bradsprojects/Digirule2U/Firmware/Source/Digirule2.X/file.c

#include "digirule2.h"

static const uint8 __section( "files" ) files[8][256] =
{
	// Slot 0 "HELLO WORLD"
	{
		0x02, 0x01, 0x05, 0x20, 0x06, 0x09, 0x00, 0x26, 
		0x00, 0xFC, 0x28, 0x02, 0xC0, 0x1E, 0x06, 0x28, 
		0x05, 0x00, 0x00, 0x00, 0x00, 0x00, 0x00, 0x00, 
		0x00, 0x00, 0x00, 0x00, 0x00, 0x00, 0x00, 0x00, 
		0x0D, 0x0A, 0x20, 0x5F, 0x20, 0x20, 0x5F, 0x20, 
		0x20, 0x20, 0x20, 0x20, 0x5F, 0x20, 0x5F, 0x20, 
		0x20, 0x20, 0x20, 0x20, 0x20, 0x5F, 0x5F, 0x20, 
		0x20, 0x20, 0x20, 0x20, 0x20, 0x5F, 0x5F, 0x20, 
		0x20, 0x20, 0x20, 0x20, 0x20, 0x20, 0x5F, 0x20, 
		0x20, 0x20, 0x20, 0x5F, 0x20, 0x20, 0x20, 0x5F, 
		0x20, 0x0D, 0x0A, 0x7C, 0x20, 0x7C, 0x7C, 0x20, 
		0x7C, 0x5F, 0x5F, 0x5F, 0x7C, 0x20, 0x7C, 0x20, 
		0x7C, 0x5F, 0x5F, 0x5F, 0x20, 0x20, 0x5C, 0x20, 
		0x5C, 0x20, 0x20, 0x20, 0x20, 0x2F, 0x20, 0x2F, 
		0x5F, 0x5F, 0x20, 0x5F, 0x20, 0x5F, 0x7C, 0x20, 
		0x7C, 0x5F, 0x5F, 0x7C, 0x20, 0x7C, 0x20, 0x7C, 
		0x20, 0x7C, 0x0D, 0x0A, 0x7C, 0x20, 0x5F, 0x5F, 
		0x20, 0x2F, 0x20, 0x2D, 0x5F, 0x29, 0x20, 0x7C, 
		0x20, 0x2F, 0x20, 0x5F, 0x20, 0x5C, 0x20, 0x20, 
		0x5C, 0x20, 0x5C, 0x2F, 0x5C, 0x2F, 0x20, 0x2F, 
		0x20, 0x5F, 0x20, 0x5C, 0x20, 0x27, 0x5F, 0x7C, 
		0x20, 0x2F, 0x20, 0x5F, 0x60, 0x20, 0x7C, 0x20, 
		0x7C, 0x5F, 0x7C, 0x0D, 0x0A, 0x7C, 0x5F, 0x7C, 
		0x7C, 0x5F, 0x5C, 0x5F, 0x5F, 0x5F, 0x7C, 0x5F, 
		0x7C, 0x5F, 0x5C, 0x5F, 0x5F, 0x5F, 0x2F, 0x20, 
		0x20, 0x20, 0x5C, 0x5F, 0x2F, 0x5C, 0x5F, 0x2F, 
		0x5C, 0x5F, 0x5F, 0x5F, 0x2F, 0x5F, 0x7C, 0x20, 
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
	
	for( addr = 0, TBLPTR = (__uint24) &files[slot][0]; addr < 256; addr++, TBLPTR++ )
	{
		if( !quiet )
		{
			address_leds = PROGRESS_BAR( addr );
			sleep_ms( 1 );		// for visual effect only
		}
		
		__asm( "TBLRD" );
		RAM[addr] = IS_REG_ADDR( addr ) ? 0 : TABLAT;
	}
}

void file_save( uint8 slot, bool_t quiet )
{
	uint16 addr;
	
	EECON1bits.CFGS = 0;		// access flash or EEPROM, not config
	EECON1bits.EEPGD = 1;		// access flash, not EEPROM
	
	for( addr = 0, TBLPTR = (__uint24) &files[slot][0]; addr < 256; addr++, TBLPTR++ )
	{
		if( !quiet )
		{
			address_leds = PROGRESS_BAR( addr );
			sleep_ms( 1 );		// for visual effect only
		}
		
		// if at FIRST byte of 64-byte block, erase
		if( (TBLPTRL & 0x3F) == 0 )
		{
			GIE = 0;
			EECON1bits.WREN = 1;
			EECON1bits.FREE = 1;
			EECON2 = 0x55;
			EECON2 = 0xAA;
			EECON1bits.WR = 1;
			EECON1bits.WREN = 0;
			GIE = 1;
		}
		
		// write holding register
		TABLAT = IS_REG_ADDR( addr ) ? 0 : RAM[addr];
		__asm( "TBLWT" );
		
		// if at LAST byte of 64-byte block, write
		if( (TBLPTRL & 0x3F) == 0x3F )
		{
			GIE = 0;
			EECON1bits.WREN = 1;
			EECON2 = 0x55;
			EECON2 = 0xAA;
			EECON1bits.WR = 1;
			EECON1bits.WREN = 0;
			GIE = 1;
		}
	}
}
